mdethmers/ESP32-Artnet-Node-receiver/Img/IMG_20250313_114016.jpg

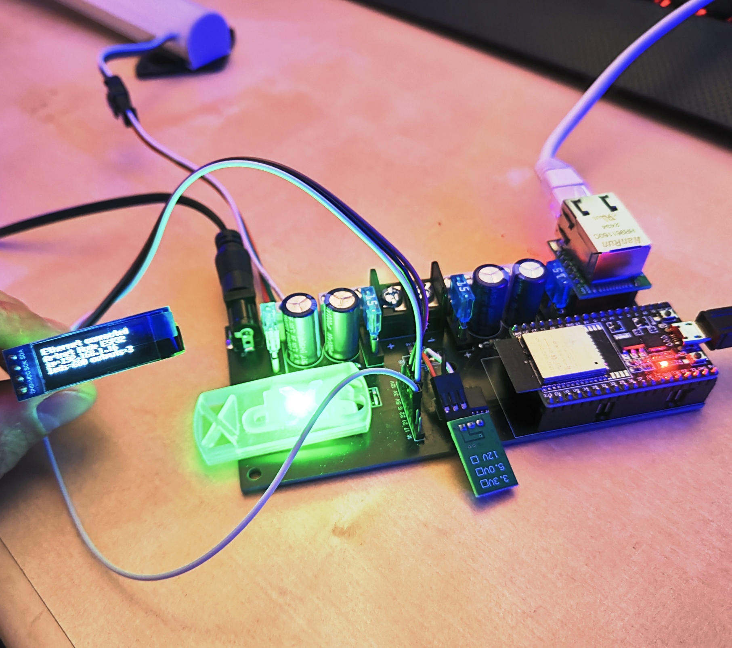
Img/IMG_20250313_114016.jpg
