mdethmers/ESP32-Artnet-Node-receiver/Img/IMG_20250623_115355.jpg

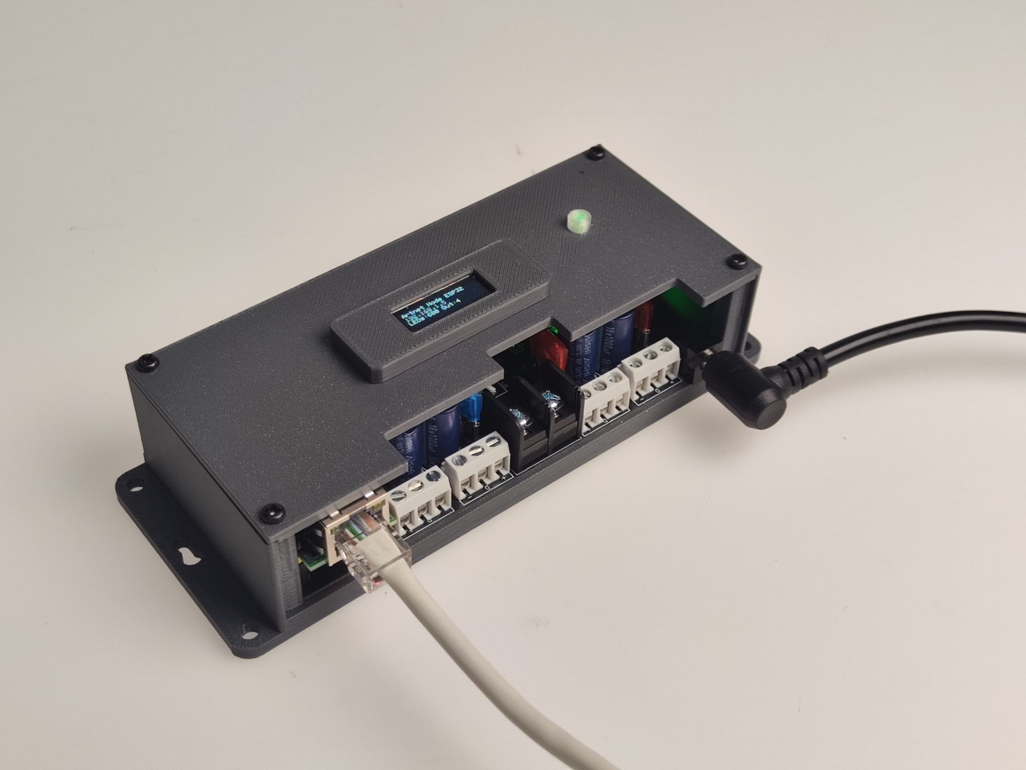
Img/IMG_20250623_115355.jpg
